alexdetrano/4CAN/pcb/revB/alex.kicad_pcb

## EAGLE design eagle/mqttSwitch2.0.sch

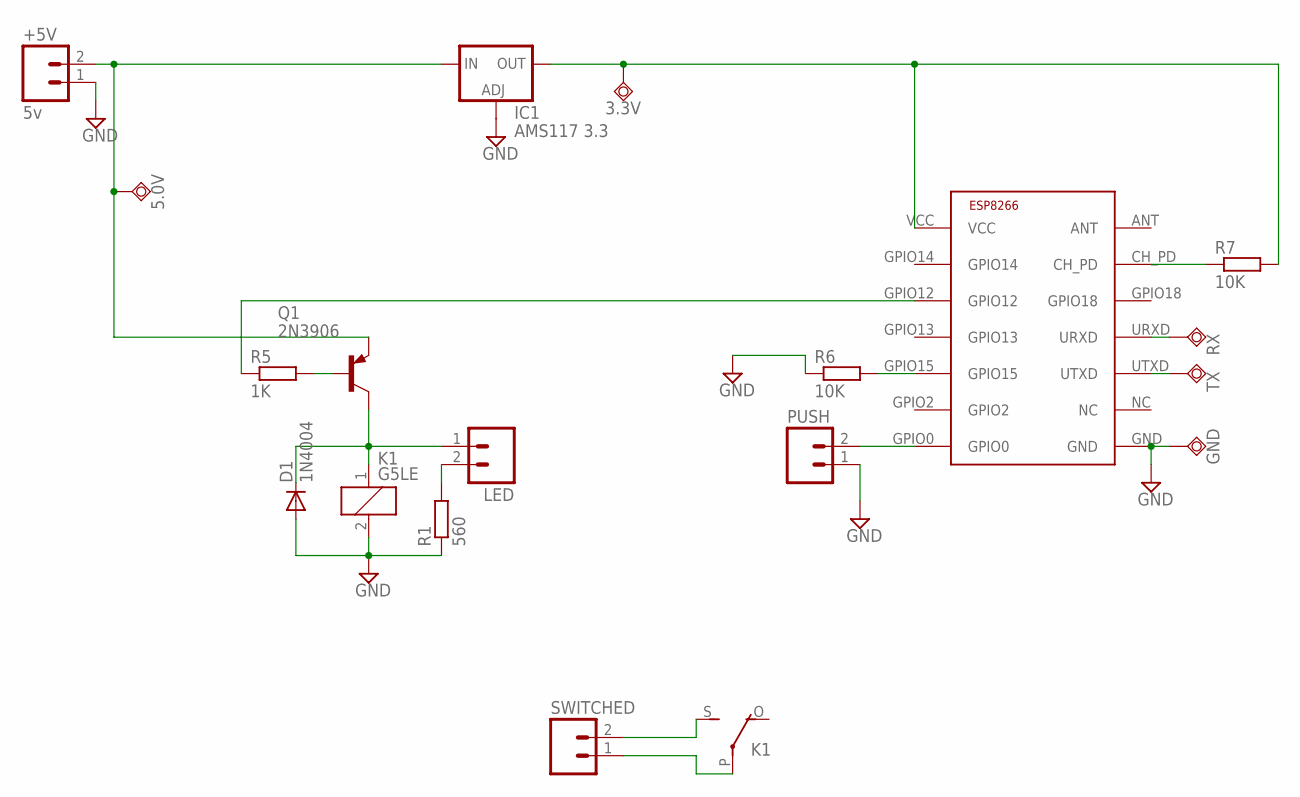
[picture p9: schematic mqttSwitch2.0.sch]

Parts:
3.3V, 5.0V: TPSQTP19R; TP19R
+5V: 5v; 1X02
D1: 1N4004; DO41-10
GND: TPSQTP19R; TP19R
IC1: AMS117 3.3; SOT223
K1: G5LE
LED: M02PTH; 1X02
PUSH: M02PTH; 1X02
Q1: 2N3906; TO92
R1: 560; R0805
R5: 1K; R0805
R6, R7: 10K; R0805
RX: TPSQTP19R; TP19R
SWITCHED: M02PTH4; 1X02_XTRA_BIG
TX: TPSQTP19R; TP19R
U$1: ESP8266; ESP-03

Connections:
GND: +5V.1, D1.A, GND.TP, IC1.1 (ADJ), K1.2, PUSH.1, R1.1, R6.1, U$1.GND
unnamed: RX.TP, U$1.URXD
unnamed: R7.1, U$1.CH_PD
unnamed: 3.3V.TP, IC1.4 (OUT), R7.2, U$1.VCC
unnamed: 5.0V.TP, +5V.2, IC1.3 (IN), Q1.3 (E)
unnamed: Q1.2 (B), R5.2
unnamed: R6.2, U$1.GPIO15
unnamed: D1.C, K1.1, LED.1, Q1.1 (C)
unnamed: TX.TP, U$1.UTXD
unnamed: PUSH.2, U$1.GPIO0
unnamed: K1.P, SWITCHED.1
unnamed: LED.2, R1.2
unnamed: R5.1, U$1.GPIO12
unnamed: K1.S, SWITCHED.2
